dossalab/minibox/firmware/src/ble.rs

use byteorder::{ByteOrder, LittleEndian};
use defmt::{debug, error, info, warn};
use embassy_futures::select::{select, Either};
use embassy_time::{Duration, Timer};
use nrf_softdevice::{
    ble::{
        self,
        central::{self, ConnectError},
        gatt_client::{self, DiscoverError},
        security::SecurityHandler,
        Address, AddressType, EncryptError, EncryptionInfo,
    },
    Softdevice,
};
use static_cell::StaticCell;

use crate::{
    indications::{IndicationStyle, LedIndicationsSignal},
    xbox::{self, ButtonFlags, JoystickData, XboxHidServiceClient, XboxHidServiceClientEvent},
};

pub struct Bonder {}

impl Default for Bonder {
    fn default() -> Self {
        Bonder {}
    }
}

impl SecurityHandler for Bonder {
    fn can_bond(&self, _conn: &nrf_softdevice::ble::Connection) -> bool {
        true
    }

    fn on_bonded(
        &self,
        _conn: &ble::Connection,
        _master_id: ble::MasterId,
        _key: EncryptionInfo,
        _peer_id: ble::IdentityKey,
    ) {
        info!("on_bonded is called!")
    }
}

#[cfg_attr(feature = "defmt", derive(defmt::Format))]
enum BleError {
    Encryption(ble::EncryptError),
    ConnectError,
    DiscoveryError,
    WriteError(gatt_client::WriteError),
    ReadError(gatt_client::ReadError),
}

impl From<ConnectError> for BleError {
    fn from(_: ConnectError) -> Self {
        return Self::ConnectError;
    }
}

impl From<DiscoverError> for BleError {
    fn from(_: DiscoverError) -> Self {
        return Self::DiscoveryError;
    }
}

impl From<gatt_client::WriteError> for BleError {
    fn from(e: gatt_client::WriteError) -> Self {
        return Self::WriteError(e);
    }
}

impl From<gatt_client::ReadError> for BleError {
    fn from(e: gatt_client::ReadError) -> Self {
        return Self::ReadError(e);
    }
}

// Scan for Xbox controllers
async fn scan(sd: &Softdevice, indications: &'static LedIndicationsSignal) -> Option<Address> {
    let config = central::ScanConfig::default();
    let timeout = Duration::from_secs(10);

    let do_scan = async || loop {
        indications.signal(IndicationStyle::BlinkFast);

        let ret = central::scan(sd, &config, |params| unsafe {
            let payload = core::slice::from_raw_parts(params.data.p_data, params.data.len as usize);

            if xbox::is_xbox_controller(payload) {
                let addr = Address::new(AddressType::Public, params.peer_addr.addr);
                info!("found controller {:?}", addr);
                Some(addr)
            } else {
                None
            }
        })
        .await;

        match ret {
            Ok(addr) => return addr,
            Err(e) => {
                error!("scan error - {}", e);
                Timer::after_millis(100).await;
            }
        }
    };

    info!(
        "scanning for Xbox controllers (timeout is {}s)...",
        timeout.as_secs()
    );

    match select(do_scan(), Timer::after(timeout)).await {
        Either::First(address) => Some(address),
        Either::Second(_) => {
            warn!("scanning timed out");
            None
        }
    }
}

async fn wait_connection(
    sd: &Softdevice,
    addr: Address,
    bonder: &'static Bonder,
    indications: &'static LedIndicationsSignal,
) -> Result<(), BleError> {
    let whitelist = &[&addr];
    let mut config = central::ConnectConfig::default();
    config.scan_config.whitelist = Some(whitelist);

    info!("connecting to device.. {}", addr);

    indications.signal(IndicationStyle::BlinkSlow);

    let conn = central::connect_with_security(sd, &config, bonder).await?;
    match conn.encrypt() {
        Ok(_) => info!("connection encrypted!"),

        Err(EncryptError::PeerKeysNotFound) => {
            info!("no peer keys, request pairing");

            match conn.request_pairing() {
                Ok(_) => info!("pairing done"),
                Err(e) => error!("pairing not done {}", e),
            }
        }

        Err(e) => {
            error!("unable to encrypt the connection");
            return Err(BleError::Encryption(e));
        }
    };

    info!("connected");

    let client: XboxHidServiceClient = gatt_client::discover(&conn).await?;

    debug!("services discovered!");

    client.hid_report_cccd_write(true).await?;

    debug!("notifications enabled!");

    // XXX: would be cool to read and dynamically parse report map
    // let report_map = client.hid_report_map_read().await?;
    // info!("report map is {:x}", report_map);

    // All ready, we're connected
    indications.signal(IndicationStyle::Disabled);

    gatt_client::run(&conn, &client, |event| match event {
        XboxHidServiceClientEvent::HidReportNotification(val) => {
            let button_mask = LittleEndian::read_u24(&val[13..16]);

            let x1 = LittleEndian::read_u16(&val[0..2]);
            let y1 = LittleEndian::read_u16(&val[2..4]);
            let x2 = LittleEndian::read_u16(&val[4..6]);
            let y2 = LittleEndian::read_u16(&val[6..8]);

            let t1 = LittleEndian::read_u16(&val[8..10]);
            let t2 = LittleEndian::read_u16(&val[10..12]);

            let jd = JoystickData {
                j1: (x1, y1),
                j2: (x2, y2),
                t1,
                t2,
                buttons: ButtonFlags::from_bits_truncate(button_mask),
            };

            info!("jd: {}", jd);
        }
    })
    .await;

    Ok(())
}

#[embassy_executor::task]
pub async fn run(sd: &'static Softdevice, indications: &'static LedIndicationsSignal) {
    static BONDER: StaticCell<Bonder> = StaticCell::new();

    let bonder = BONDER.init(Bonder::default());

    loop {
        if let Some(address) = scan(sd, indications).await {
            match wait_connection(sd, address, bonder, indications).await {
                Err(e) => error!("unable to handle connection - {}", e),
                Ok(_) => {}
            }
        }
    }
}
